VJLeong/co2_project/Capacitor/capacitor_measure.asc

C1: cap; 60n
C2: cap; 100n
R1: res; 1K
R2: res; 10K
U1: NE555
V1: voltage; 5
Named nets: 0
.tran 10m
