VJLeong/co2_project/Capacitor/Draft1.asc

M1: nmos4
M2: nmos4
M3: pmos4
M4: pmos4
M5: pmos4
V1: voltage; 5
Named nets: 0, Vss, C, D, E, B, A
