VJLeong/co2_project/Capacitor/heatpad.asc

C5: cap; 100n
Cbyp1: cap; 10µ
Cbyp2: cap; 10µ
GPIO: voltage; 2.5; Rser=100
R1: res; 250
R2: res; 18
R3: res; 1k
R4: res; 1k
R5: res; 2.7k
R6: res; 1k
U1: TL974
U2: TL974
VCC1: voltage; 15
VEE1: voltage; 15
Named nets: V+, V-, 0
.tran 10m
