VJLeong/co2_project/Interface1.cydsn/codegentemp/Heater_ENA_aliases.h

/*******************************************************************************
* File Name: Heater_ENA.h  
* Version 2.20
*
* Description:
*  This file contains the Alias definitions for Per-Pin APIs in cypins.h. 
*  Information on using these APIs can be found in the System Reference Guide.
*
* Note:
*
********************************************************************************
* Copyright 2008-2015, Cypress Semiconductor Corporation.  All rights reserved.
* You may use this file only in accordance with the license, terms, conditions, 
* disclaimers, and limitations in the end user license agreement accompanying 
* the software package with which this file was provided.
*******************************************************************************/

#if !defined(CY_PINS_Heater_ENA_ALIASES_H) /* Pins Heater_ENA_ALIASES_H */
#define CY_PINS_Heater_ENA_ALIASES_H

#include "cytypes.h"
#include "cyfitter.h"


/***************************************
*              Constants        
***************************************/
#define Heater_ENA_0			(Heater_ENA__0__PC)
#define Heater_ENA_0_INTR	((uint16)((uint16)0x0001u << Heater_ENA__0__SHIFT))

#define Heater_ENA_INTR_ALL	 ((uint16)(Heater_ENA_0_INTR))

#endif /* End Pins Heater_ENA_ALIASES_H */


/* [] END OF FILE */
